Broosky/Patchworks/KiCad/Patchworks.kicad_sch

## KiCad design KiCad/Patchworks.kicad_sch (2026-04-23)

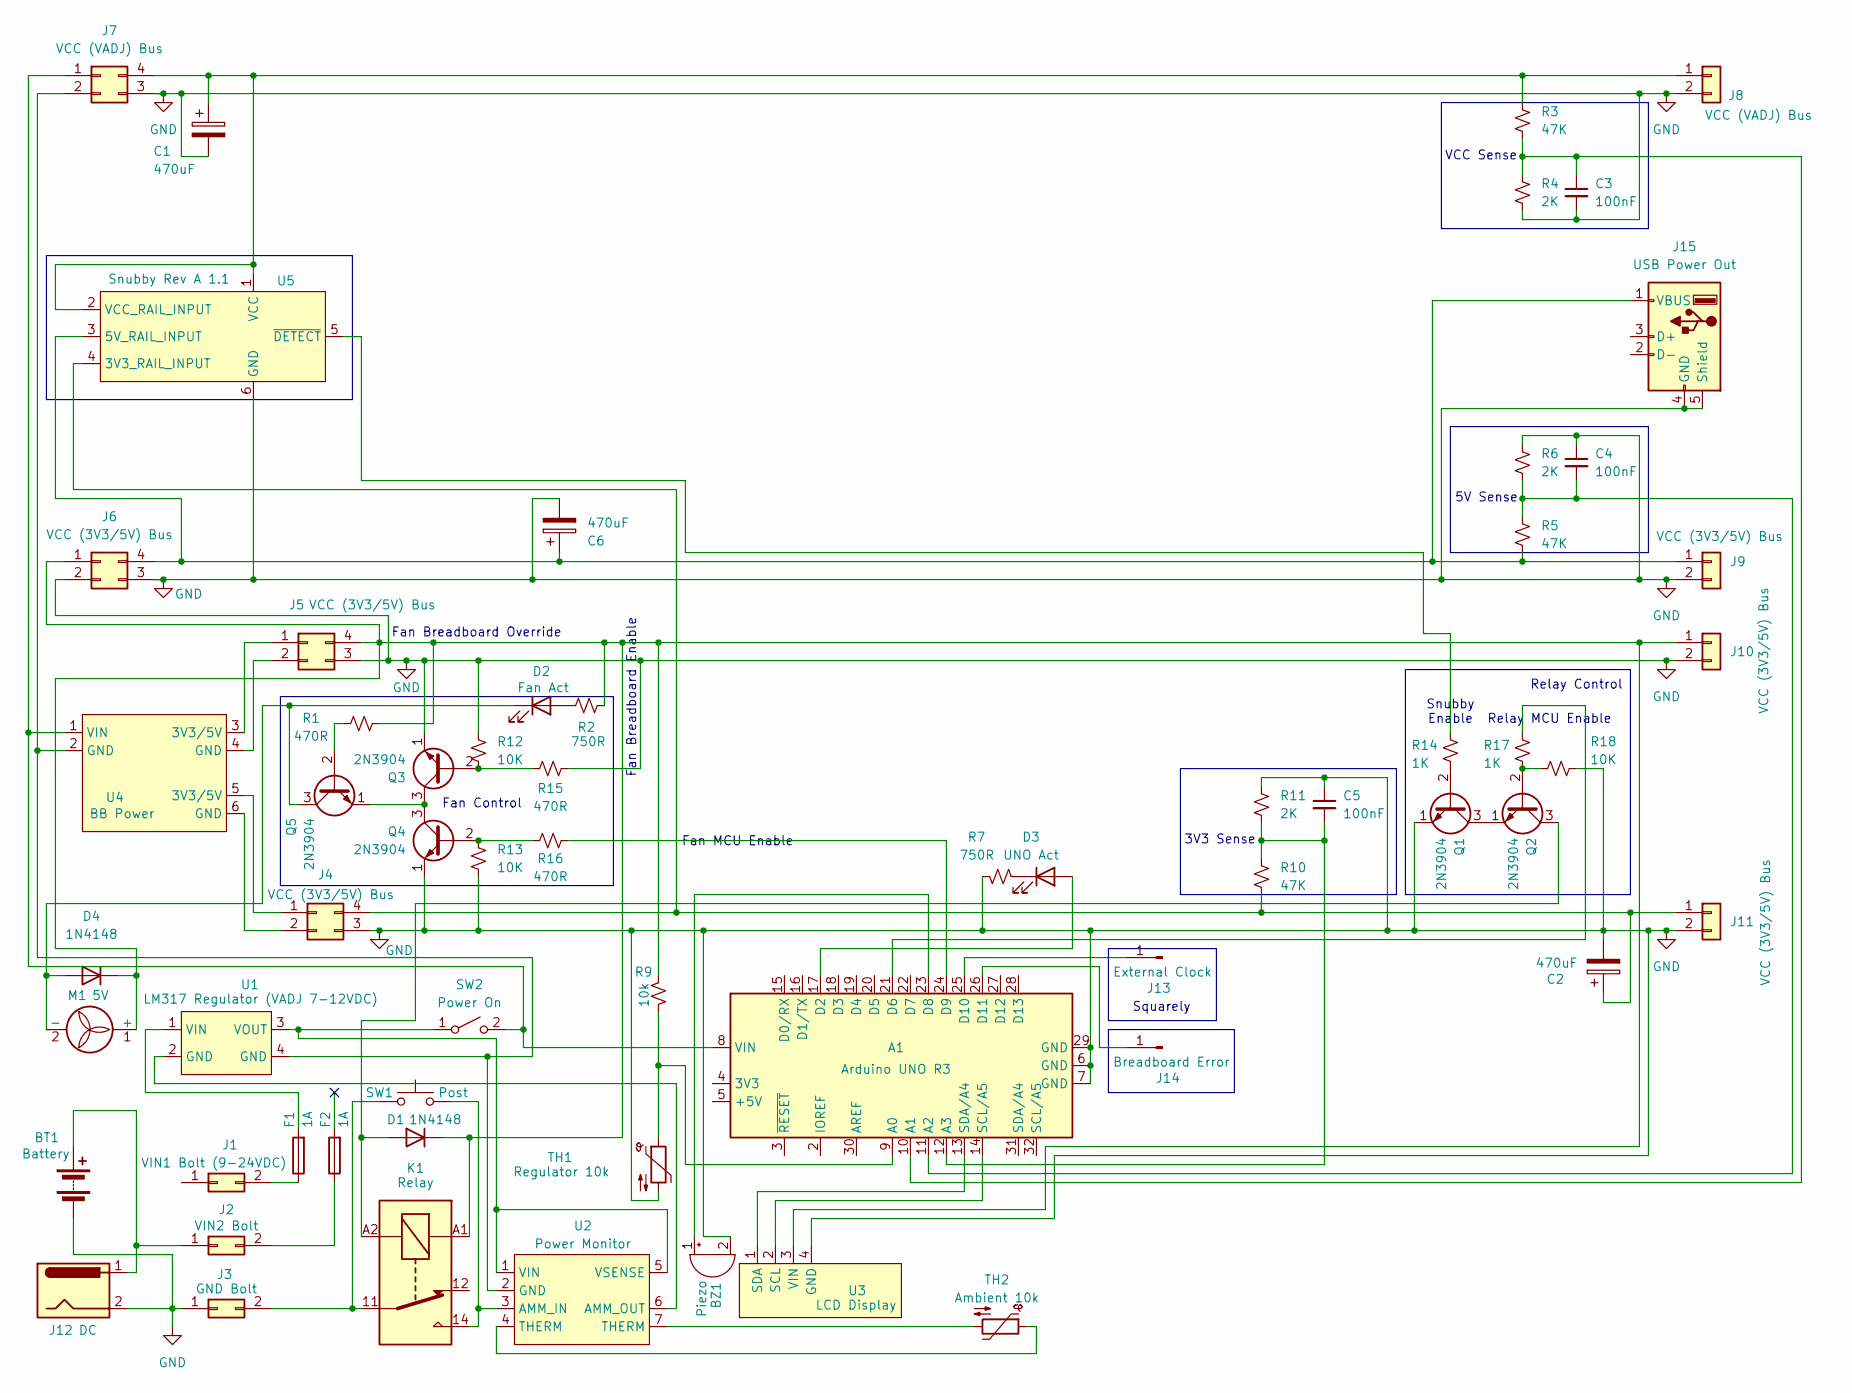
[picture p7: schematic Patchworks.kicad_sch]

Parts:
A1: Arduino UNO R3; Arduino_UNO_R3
BT1: Battery
BZ1: Piezo
C1, C2, C6: 470uF
C3, C4, C5: 100nF
D1: 1N4148; D_DO-41_SOD81_P10.16mm_Horizontal
D2: Fan Act
D3: UNO Act
D4: 1N4148; D_DO-35_SOD27_P7.62mm_Horizontal
F1, F2: 1A
J1: VIN1 Bolt (9-24VDC)
J2: VIN2 Bolt
J3: GND Bolt
J4, J5, J6, J9, J10, J11: VCC (3V3/5V) Bus
J7, J8: VCC (VADJ) Bus
J12: DC
J13: External Clock
J14: Breadboard Error
J15: USB Power Out
K1: Relay
M1: 5V
Q1, Q2, Q3, Q4, Q5: 2N3904; TO-92_Inline
R1, R15, R16: 470R
R2, R7: 750R
R3, R5, R10: 47K
R4, R6, R11: 2K
R9: 10k
R12, R13, R18: 10K
R14, R17: 1K
SW1: Post
SW2: Power On
TH1: Regulator 10k
TH2: Ambient 10k
U1: LM317 Regulator (VADJ 7-12VDC)
U2: Power Monitor
U3: LCD Display
U4: BB Power
U5: (no value)

Connections:
GND: A1.6 (GND), A1.7 (GND), A1.29 (GND), BT1.2 (-), BZ1.2 (-), C1.2, C2.2, C3.2, C4.1, C5.1, C6.2, J3.1, J4.3, J5.3, J6.2, J6.3, J7.3, J8.2, J9.2, J10.2, J11.2, J12.2, J15.4 (GND), J15.5 (Shield), Q1.1 (E), Q3.1 (E), Q4.1 (E), R4.2, R6.1, R7.1, R11.1, R12.1, R13.2, R15.2, R18.2, TH1.2, U3.4 (GND), U5.6 (GND)
unnamed: A1.8 (VIN), J7.1, SW2.2 (B), U4.1 (VIN)
unnamed: A1.9 (A0), R9.2, TH1.1
unnamed: A1.10 (A1), C3.1, R3.2, R4.1
unnamed: A1.11 (A2), C4.2, R5.1, R6.2
unnamed: A1.12 (A3), C5.2, R10.1, R11.2
unnamed: A1.13 (SDA/A4), U3.1 (SDA)
unnamed: A1.14 (SCL/A5), U3.2 (SCL)
unnamed: A1.17 (D2), D3.2 (A)
unnamed: A1.21 (D6), R17.1
unnamed: A1.23 (D8), BZ1.1 (+)
unnamed: A1.24 (D9), R16.2
unnamed: A1.25 (D10), J13.1
unnamed: A1.26 (D11), J14.1
unnamed: BT1.1 (+), J2.1, J12.1
unnamed: C1.1, J7.4, J8.1, R3.1, U5.1 (VCC), U5.2 (VCC_RAIL_INPUT)
unnamed: C2.1, J4.4, J11.1, R10.2, U5.4 (3V3_RAIL_INPUT)
unnamed: C6.1, J6.4, J9.1, J15.1 (VBUS), R5.2, U5.3 (5V_RAIL_INPUT)
unnamed: D1.1 (K), D4.1 (K), J5.4, J6.1, J10.1, K1.A1, M1.1 (+), R1.2, R2.1, R9.1, U3.3 (VIN)
unnamed: D1.2 (A), K1.A2, Q2.3 (C)
unnamed: D2.1 (K), D4.2 (A), M1.2 (-), Q5.3 (C)
unnamed: D2.2 (A), R2.2
unnamed: D3.1 (K), R7.2
unnamed: F1.1, J1.2
unnamed: F1.2, U1.1 (VIN)
unnamed: F2.1, J2.2
unnamed: J3.2, K1.11, SW1.1
unnamed: J4.1, U4.5 (3V3/5V)
unnamed: J4.2, U4.6 (GND)
unnamed: J5.1, U4.3 (3V3/5V)
unnamed: J5.2, U4.4 (GND)
unnamed: J7.2, U1.4 (GND), U2.2 (GND), U4.2 (GND)
unnamed: K1.14, SW1.2, U2.3 (AMM_IN)
unnamed: Q1.2 (B), R14.2
unnamed: Q1.3 (C), Q2.1 (E)
unnamed: Q2.2 (B), R17.2, R18.1
unnamed: Q3.2 (B), R12.2, R15.1
unnamed: Q3.3 (C), Q4.3 (C), Q5.1 (E)
unnamed: Q4.2 (B), R13.1, R16.1
unnamed: Q5.2 (B), R1.1
unnamed: R14.1, U5.5 (~DETECT)
unnamed: SW2.1 (A), U1.3 (VOUT), U2.1 (VIN), U2.5 (VSENSE)
unnamed: TH2.1, U2.4 (THERM)
unnamed: TH2.2, U2.7 (THERM)
unnamed: U1.2 (GND), U2.6 (AMM_OUT)

Notes on the sheet:
Fan Control
3V3 Sense
Squarely
Relay MCU Enable
Relay Control
Fan Breadboard Override
Fan MCU Enable
VCC Sense
Fan Breadboard Enable
5V Sense
Snubby Enable
