Broosky/Patchworks/melody.cpp

/////////////////////////////////////////////////////////////////////////////////////////////////////////////////////////////
// Project: Patchworks                                                                                                     //
// Author: Jeffrey Bednar                                                                                                  //
// Copyright (c) Illusion Interactive, 2011 - 2026.                                                                        //
/////////////////////////////////////////////////////////////////////////////////////////////////////////////////////////////
#include "Headers/melody.h"
/////////////////////////////////////////////////////////////////////////////////////////////////////////////////////////////
const MELODY_T melodyTest = {
  .frequency = 1000,
  .durationMs = 50,
  .cycles = 3,
  .toneCycleDelayMs = 100,
  .pauseBeforeReturn = true
};
/////////////////////////////////////////////////////////////////////////////////////////////////////////////////////////////
const MELODY_T melodyFanOn = {
  .frequency = 2000,
  .durationMs = 50,
  .cycles = 3,
  .toneCycleDelayMs = 100,
  .pauseBeforeReturn = true
};
/////////////////////////////////////////////////////////////////////////////////////////////////////////////////////////////
const MELODY_T melodyFanOff = {
  .frequency = 2000,
  .durationMs = 50,
  .cycles = 1,
  .toneCycleDelayMs = 100,
  .pauseBeforeReturn = true
};
/////////////////////////////////////////////////////////////////////////////////////////////////////////////////////////////
const MELODY_T melodyVoltageThresholds = {
  .frequency = 1750,
  .durationMs = 50,
  .cycles = 3,
  .toneCycleDelayMs = 100,
  .pauseBeforeReturn = true
};
/////////////////////////////////////////////////////////////////////////////////////////////////////////////////////////////
const MELODY_T melodyMaxTemp = {
  .frequency = 3000,
  .durationMs = 50,
  .cycles = 3,
  .toneCycleDelayMs = 100,
  .pauseBeforeReturn = true
};
/////////////////////////////////////////////////////////////////////////////////////////////////////////////////////////////
const MELODY_T melodyShutdown = {
  .frequency = 4000,
  .durationMs = 1000,
  .cycles = 15,
  .toneCycleDelayMs = 250,
  .pauseBeforeReturn = true
};
/////////////////////////////////////////////////////////////////////////////////////////////////////////////////////////////
